pixelthorn/rackstack/rack-mount/angle-bracket/angle_bracket.png

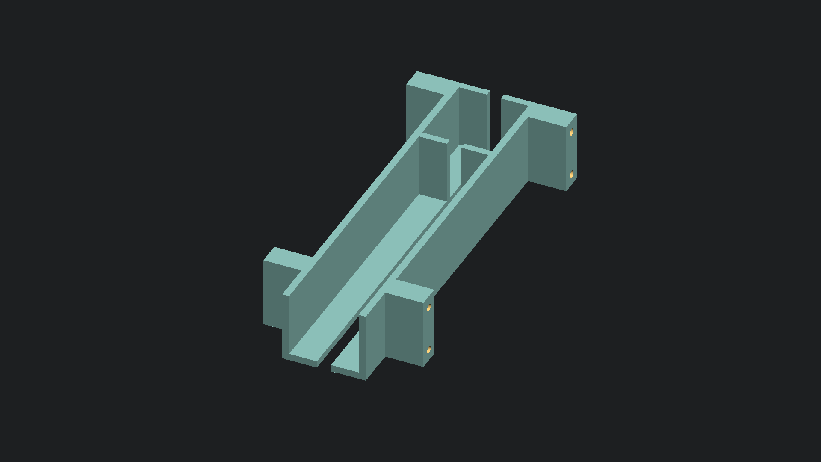
rack-mount/angle-bracket/angle_bracket.png
