pixelthorn/rackstack/rack-mount/boxes/enclosed-box/enclosed-box.png

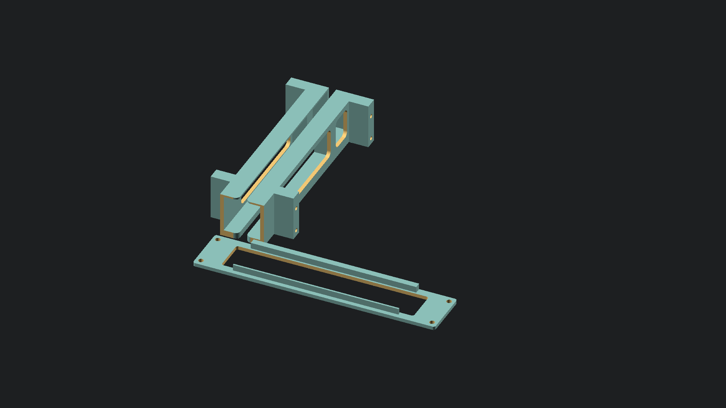
rack-mount/boxes/enclosed-box/enclosed-box.png
