pixelthorn/rackstack/rack-mount/boxes/rpi-sbc-simple-box/frontPlate.png

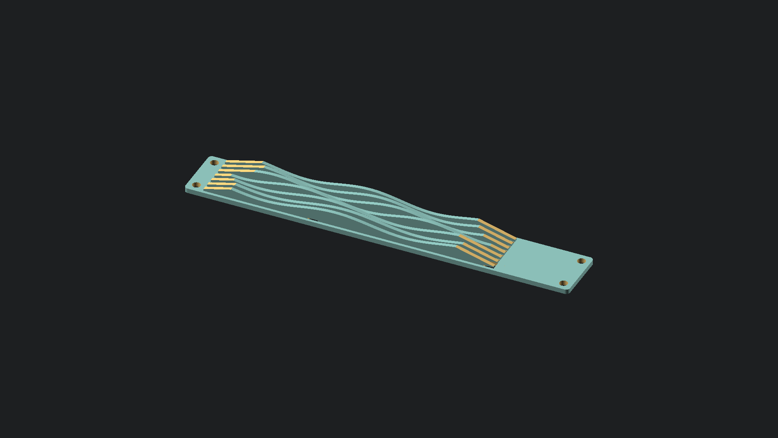
rack-mount/boxes/rpi-sbc-simple-box/frontPlate.png
