pixelthorn/rackstack/rack-mount/boxes/rpi-sbc-simple-box/top.png

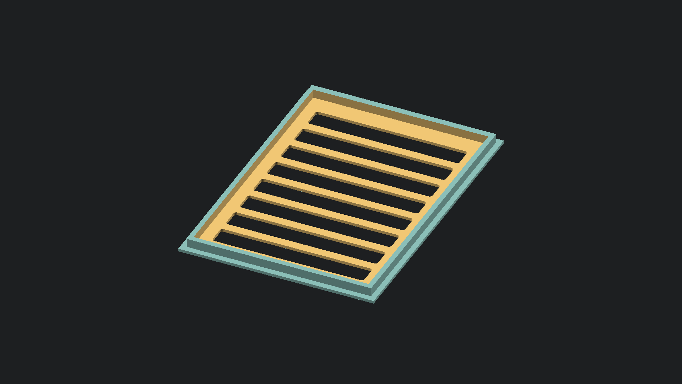
rack-mount/boxes/rpi-sbc-simple-box/top.png
