pixelthorn/rackstack/rack-mount/trays/LG-Slim_DVD-Tray/LG_Slim_DVD_Tray.png

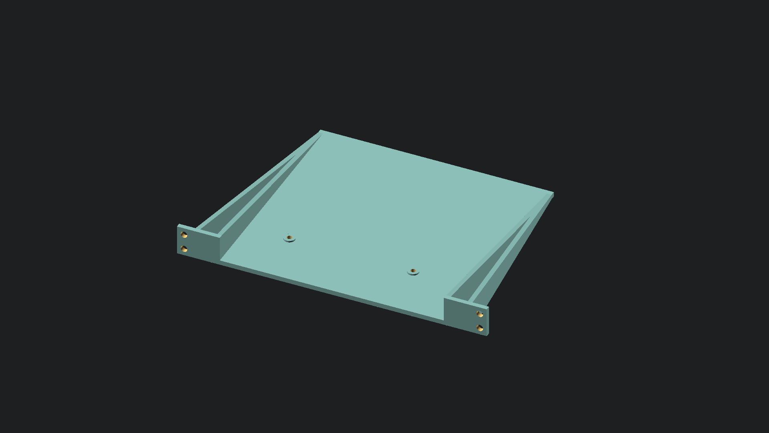
rack-mount/trays/LG-Slim_DVD-Tray/LG_Slim_DVD_Tray.png
